tkgktyk/analog-mimic/firmware/targets/mimic0x/Inc/mimic0x_msp.h

/**
 ******************************************************************************
 * @file    mimic0x_msp.h
 * @author  TAKAGI Katsuyuki
 * @brief   Header for MCU Support Package (Hardware-specific initializations)
 ******************************************************************************
  * @attention
  *
  * <h2><center>&copy; Copyright (c) 2023 Puya Semiconductor Co.
  * All rights reserved.</center></h2>
  *
  * This software component is licensed by Puya under BSD 3-Clause license,
  * the "License"; You may not use this file except in compliance with the
  * License. You may obtain a copy of the License at:
  *                        opensource.org/licenses/BSD-3-Clause
  *
  ******************************************************************************
  * @attention
  *
  * <h2><center>&copy; Copyright (c) 2016 STMicroelectronics.
  * All rights reserved.</center></h2>
  *
  * This software component is licensed by ST under BSD 3-Clause license,
  * the "License"; You may not use this file except in compliance with the
  * License. You may obtain a copy of the License at:
  *                        opensource.org/licenses/BSD-3-Clause
  *
  ******************************************************************************
  */

#ifndef MIMIC0X_MSP_H
#define MIMIC0X_MSP_H

#include <stdbool.h>

/* Hardware initialization for LL drivers and generic GPIOs */
void Mimic_I2C1_Hardware_Init(void);
void Mimic_GPIO_Hardware_Init(void);

/* Hardware specific control abstractions */
void Mimic_SetReadyLED(bool is_on);

#endif /* MIMIC0X_MSP_H */
